SirSundays/capactive-soil-moisture-sensor-lora/Media/PCB.jpg

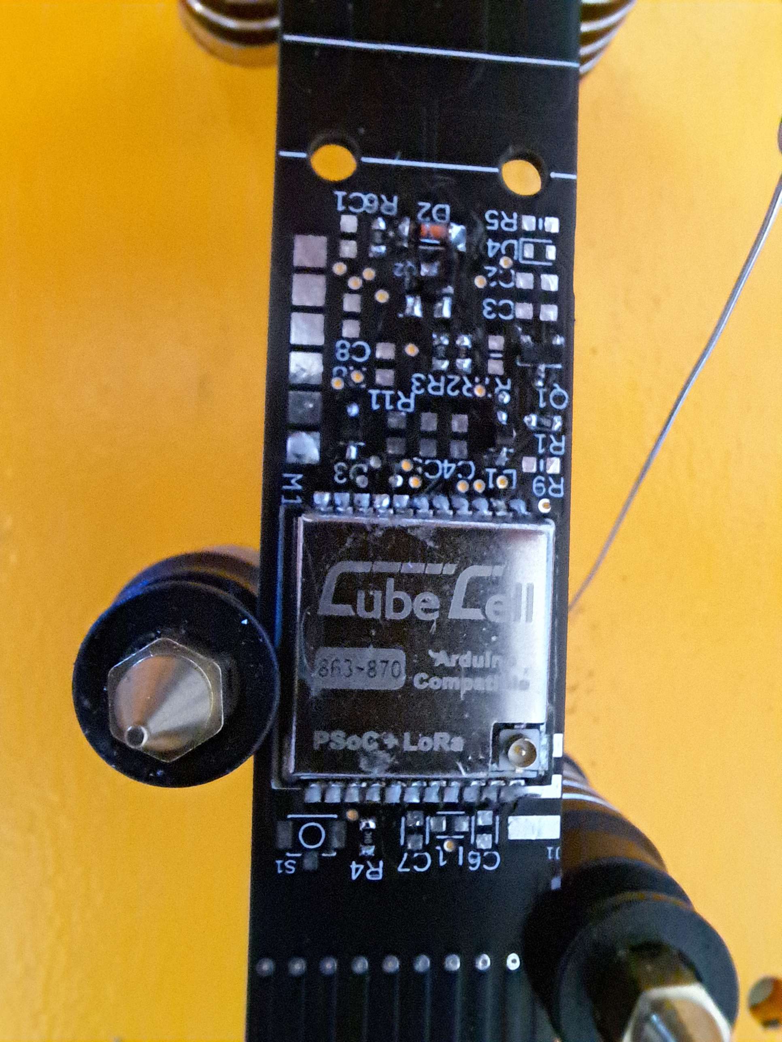
Media/PCB.jpg
