SirSundays/capactive-soil-moisture-sensor-lora/Media/Potting/20230603_204240.jpg

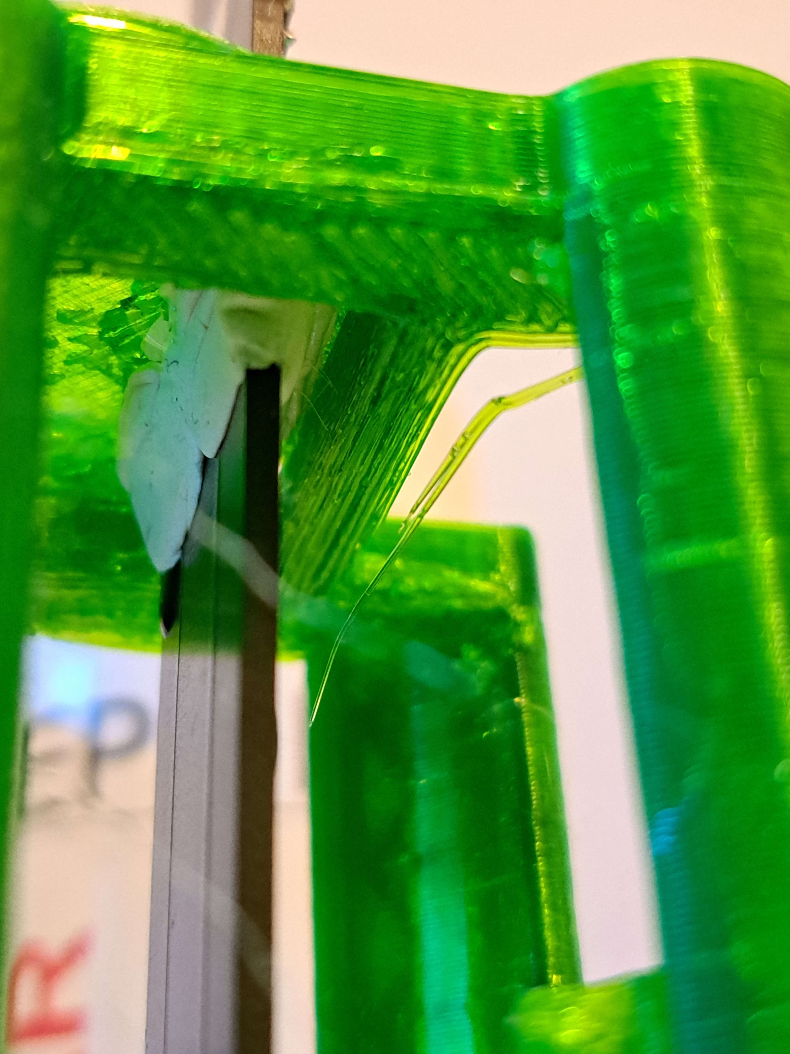
Media/Potting/20230603_204240.jpg
