SirSundays/capactive-soil-moisture-sensor-lora/Media/Potting/20230606_083855.jpg

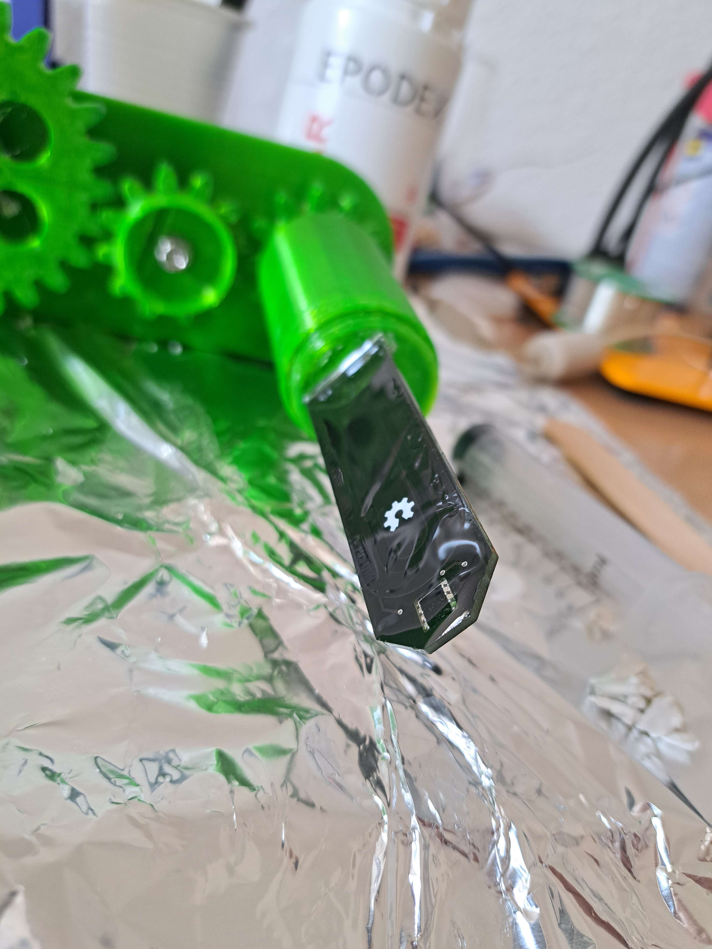
Media/Potting/20230606_083855.jpg
