SirSundays/capactive-soil-moisture-sensor-lora/Media/Potting/20230606_083947.jpg

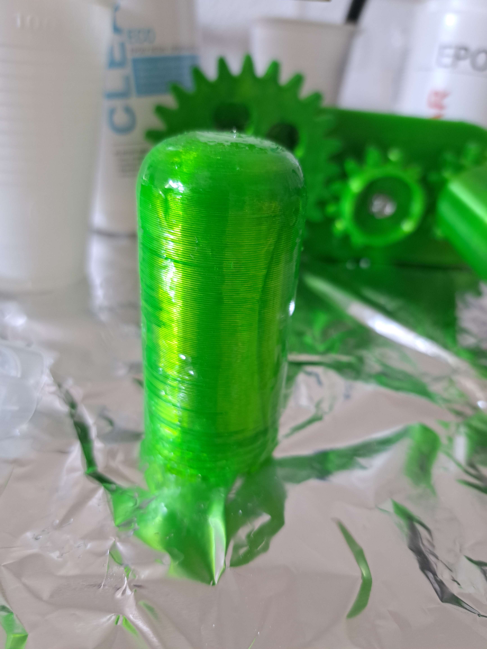
Media/Potting/20230606_083947.jpg
