SirSundays/capactive-soil-moisture-sensor-lora/Media/Potting/20240121_231839.jpg

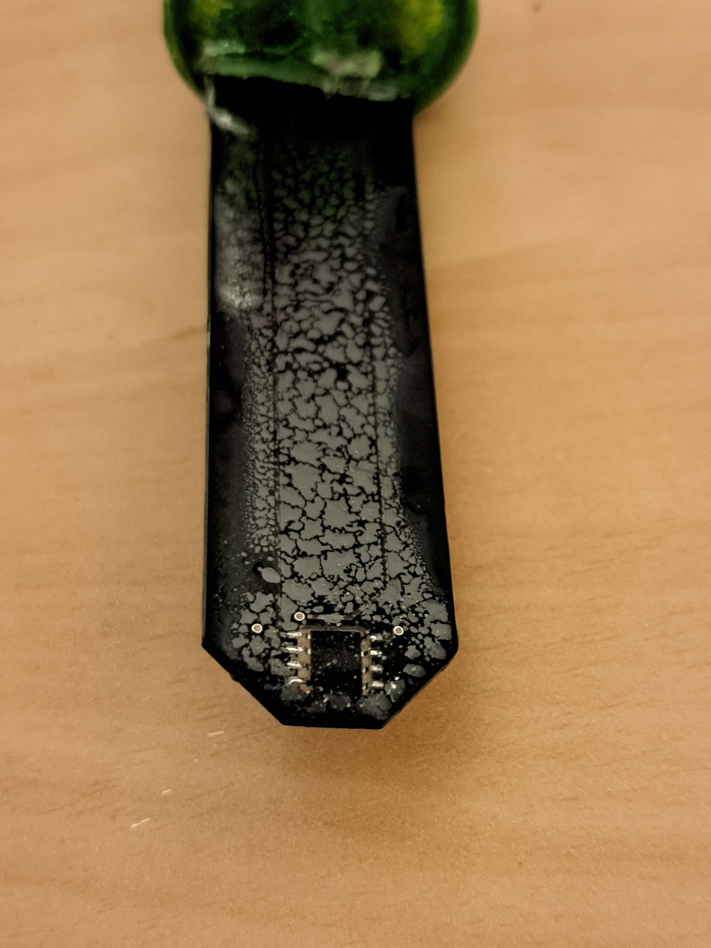
Media/Potting/20240121_231839.jpg
