SirSundays/capactive-soil-moisture-sensor-lora/Media/Potting/20240121_233238.jpg

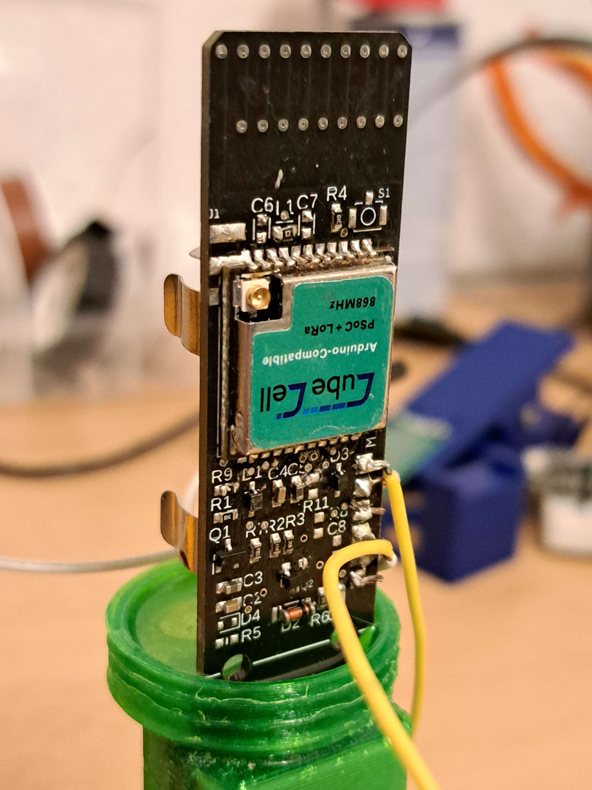
Media/Potting/20240121_233238.jpg
