SirSundays/capactive-soil-moisture-sensor-lora/Media/Potting/PCB.jpg

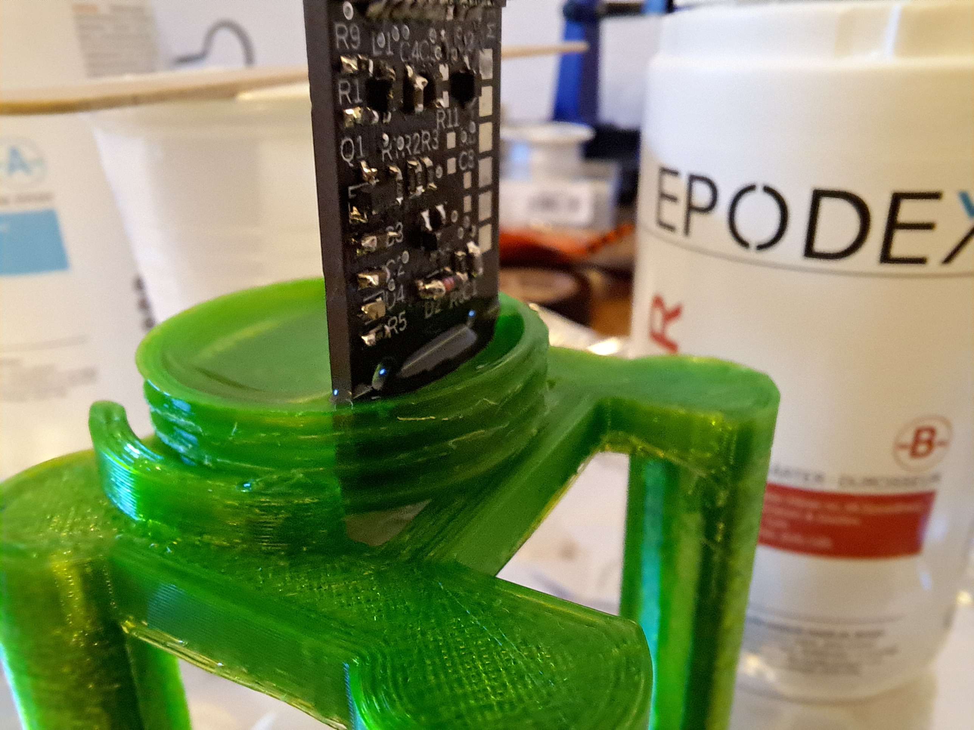
Media/Potting/PCB.jpg
