SirSundays/capactive-soil-moisture-sensor-lora/Media/Programming_Jig.jpg

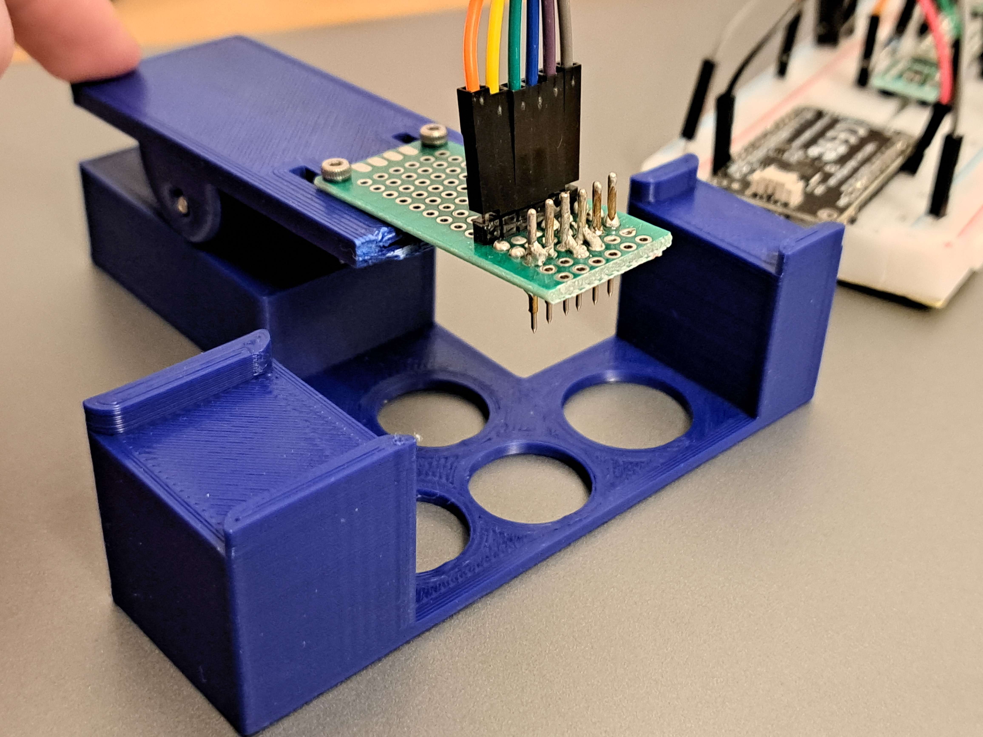
Media/Programming_Jig.jpg
