SirSundays/capactive-soil-moisture-sensor-lora/Media/Antenna Test/20230517_183743.jpg

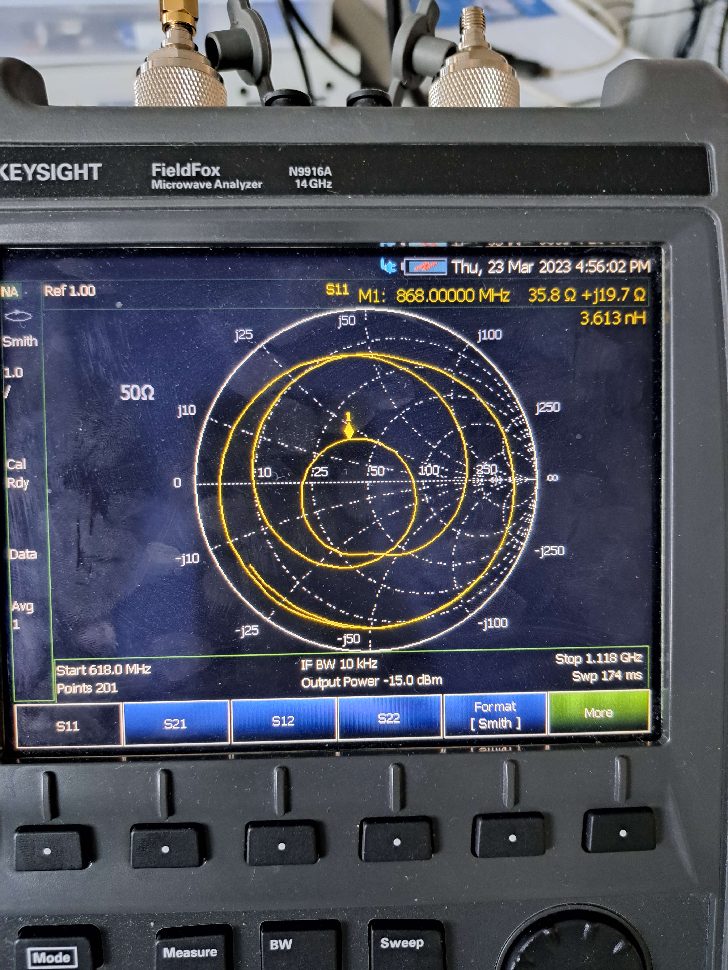
Media/Antenna Test/20230517_183743.jpg
