SirSundays/capactive-soil-moisture-sensor-lora/Media/Antenna Test/20230517_183756.jpg

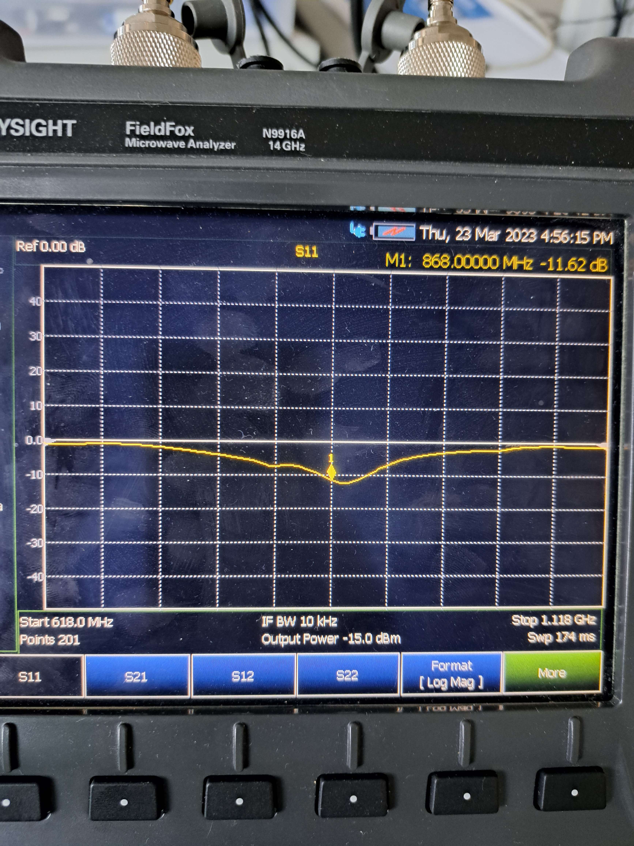
Media/Antenna Test/20230517_183756.jpg
