SirSundays/capactive-soil-moisture-sensor-lora/Media/Antenna Test/20230517_184227.jpg

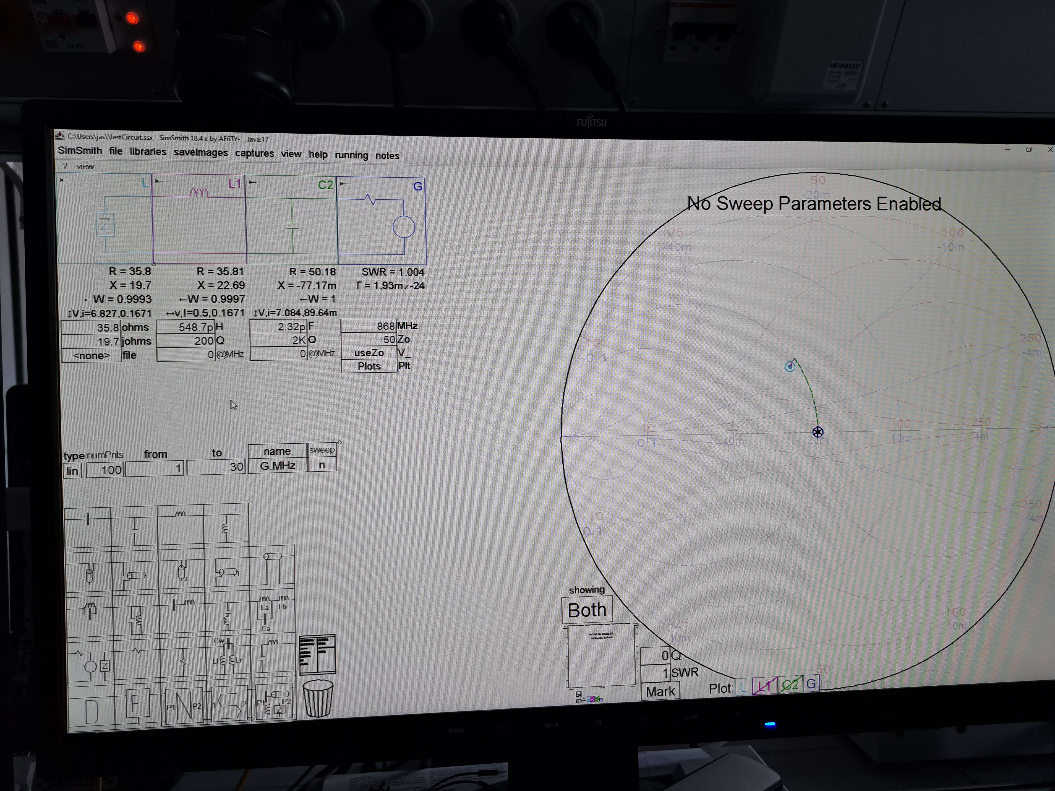
Media/Antenna Test/20230517_184227.jpg
