SirSundays/capactive-soil-moisture-sensor-lora/Media/Antenna Test/20230517_184956.jpg

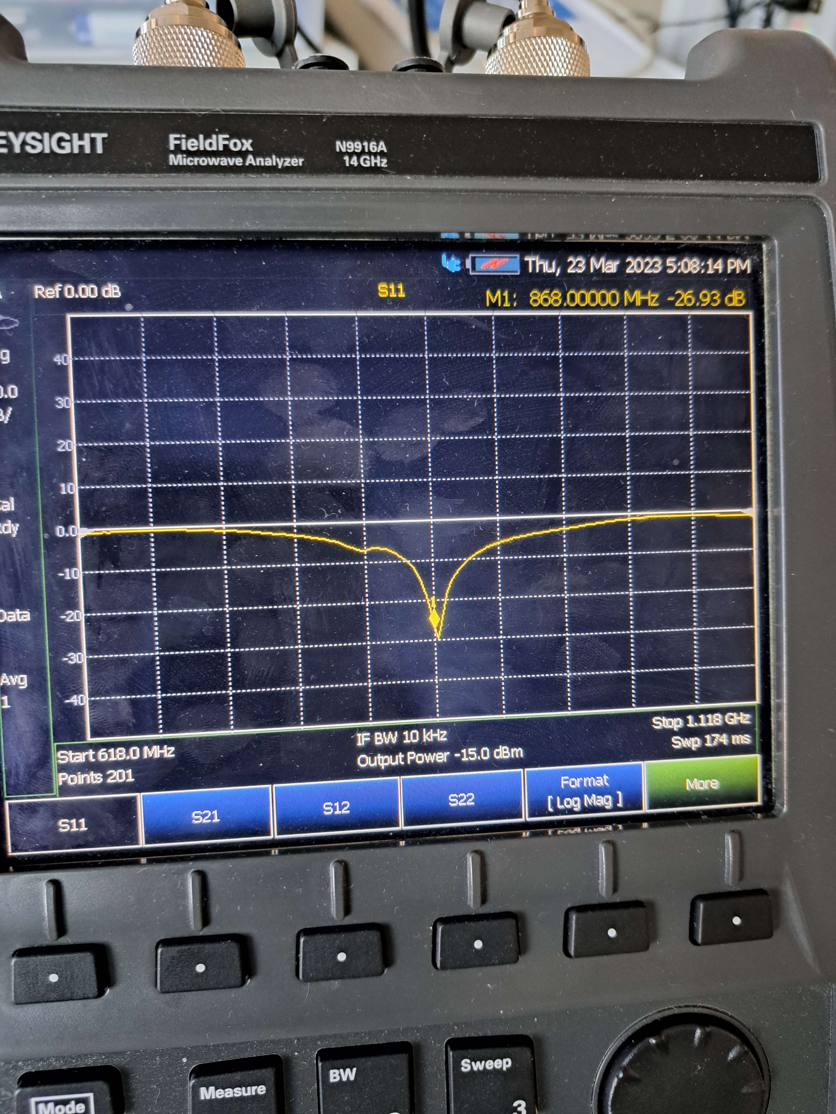
Media/Antenna Test/20230517_184956.jpg
