SirSundays/capactive-soil-moisture-sensor-lora/Media/Antenna Test/20230517_185003.jpg

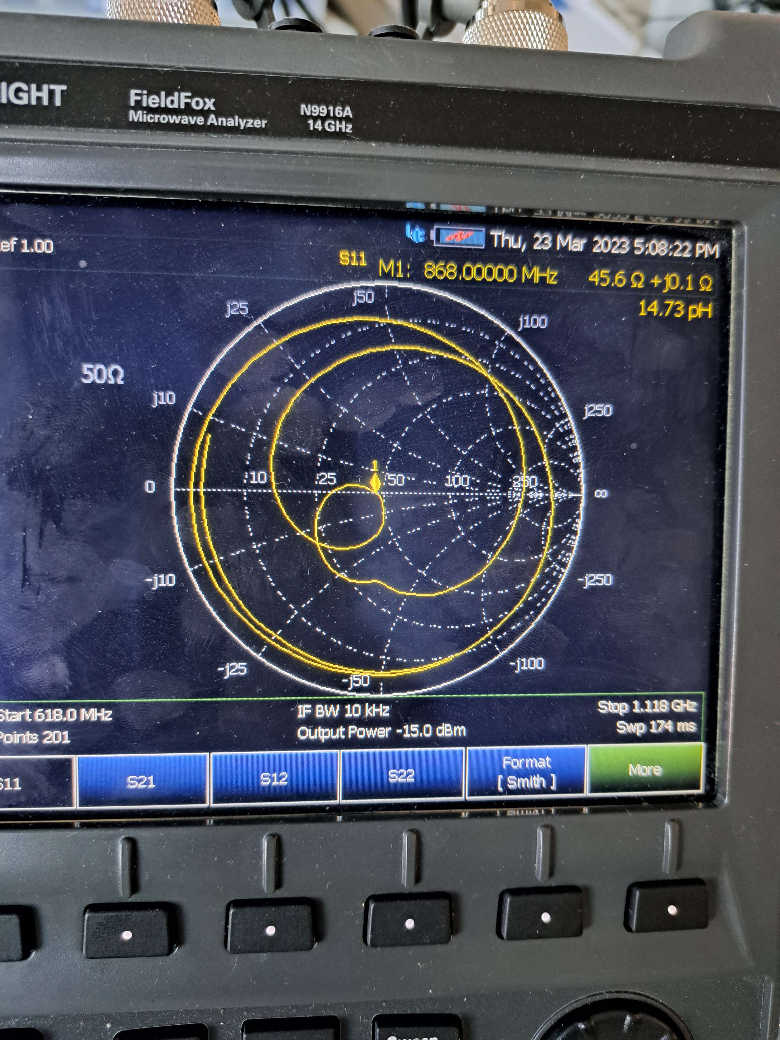
Media/Antenna Test/20230517_185003.jpg
