SirSundays/capactive-soil-moisture-sensor-lora/Media/Antenna Test/20240121_233658.jpg

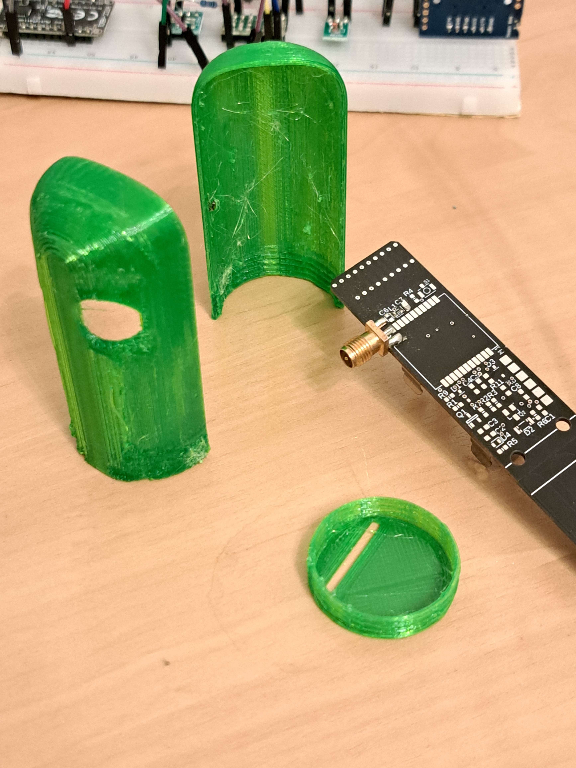
Media/Antenna Test/20240121_233658.jpg
