SirSundays/capactive-soil-moisture-sensor-lora/Media/Battery Test/20240121_231822.jpg

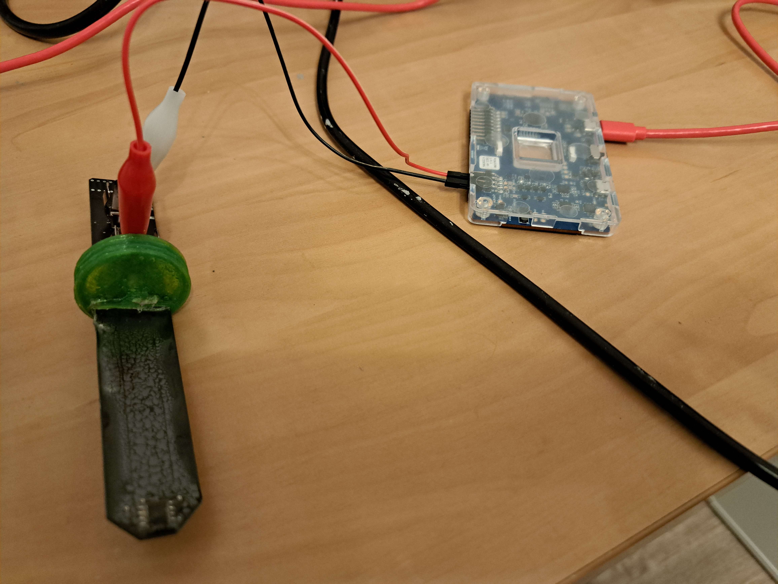
Media/Battery Test/20240121_231822.jpg
