SirSundays/capactive-soil-moisture-sensor-lora/Media/Battery Test/20240121_233023.jpg

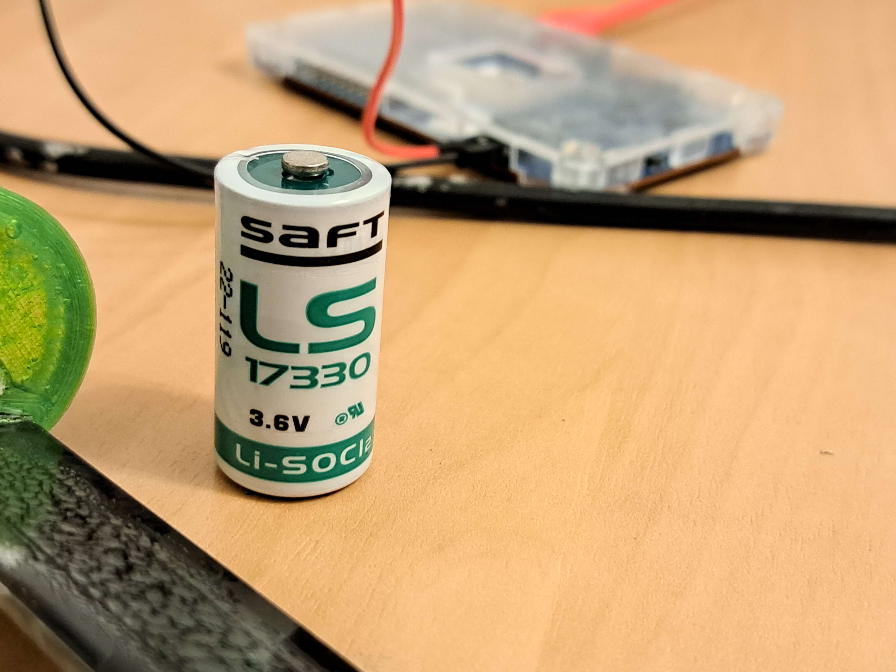
Media/Battery Test/20240121_233023.jpg
