SirSundays/capactive-soil-moisture-sensor-lora/Media/Circuit Evaluation/20230502_162933.jpg

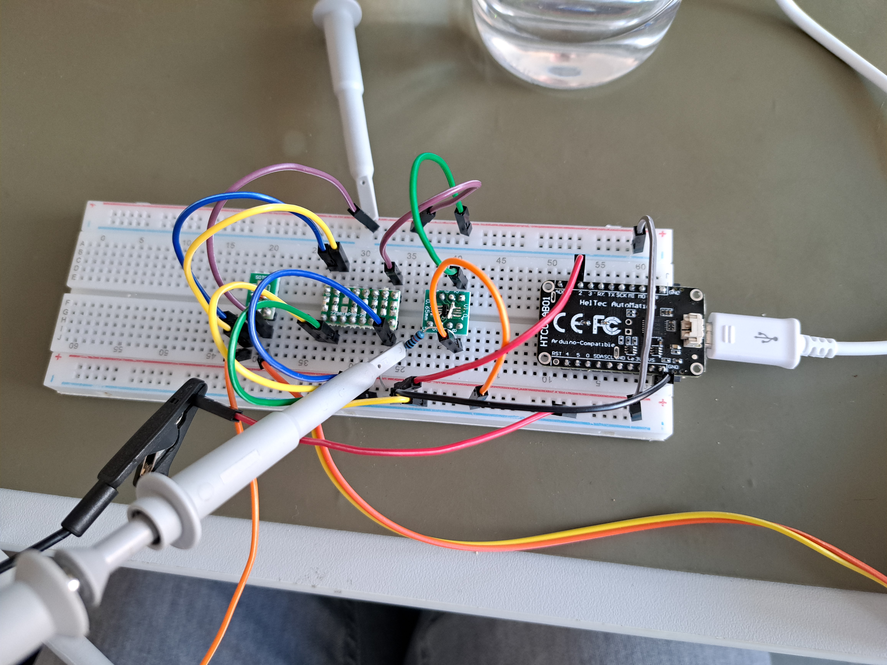
Media/Circuit Evaluation/20230502_162933.jpg
