SirSundays/capactive-soil-moisture-sensor-lora/Media/Circuit Evaluation/20230502_163412.jpg

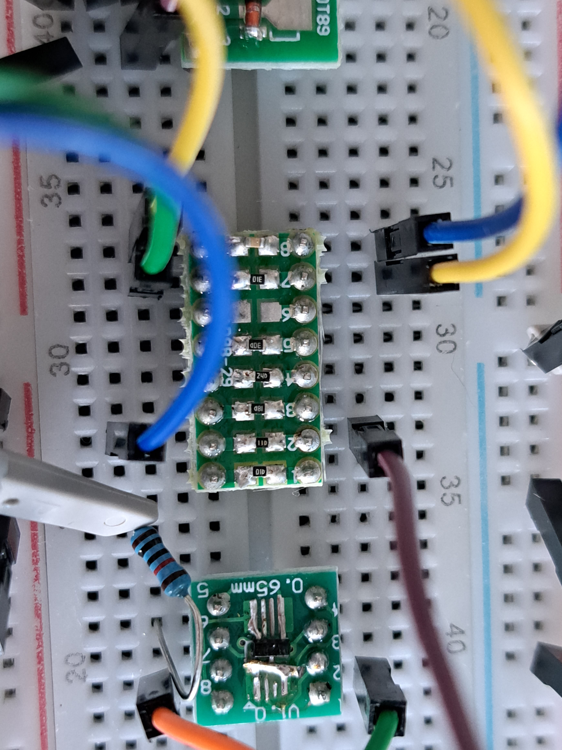
Media/Circuit Evaluation/20230502_163412.jpg
