SirSundays/capactive-soil-moisture-sensor-lora/Media/First PCB Tests/20230424_172208.jpg

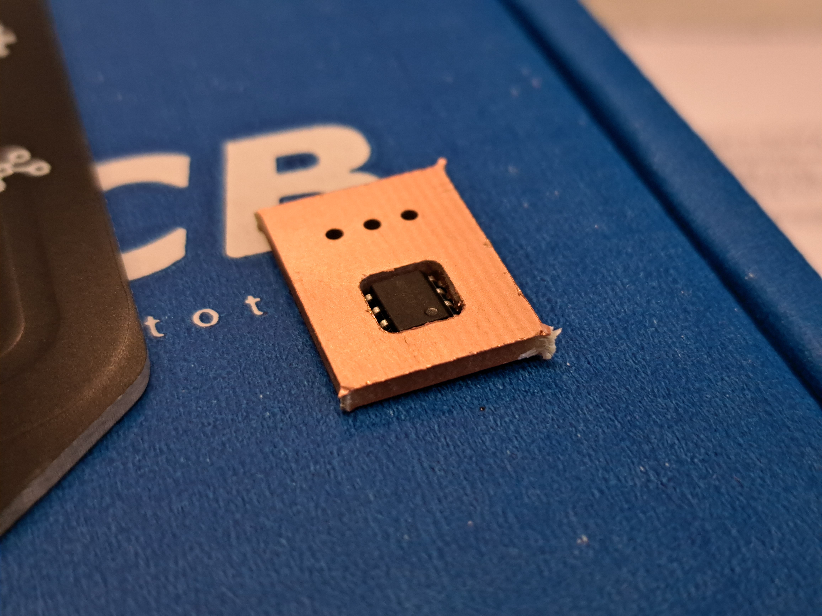
Media/First PCB Tests/20230424_172208.jpg
