SirSundays/capactive-soil-moisture-sensor-lora/Media/First PCB Tests/20230424_172226.jpg

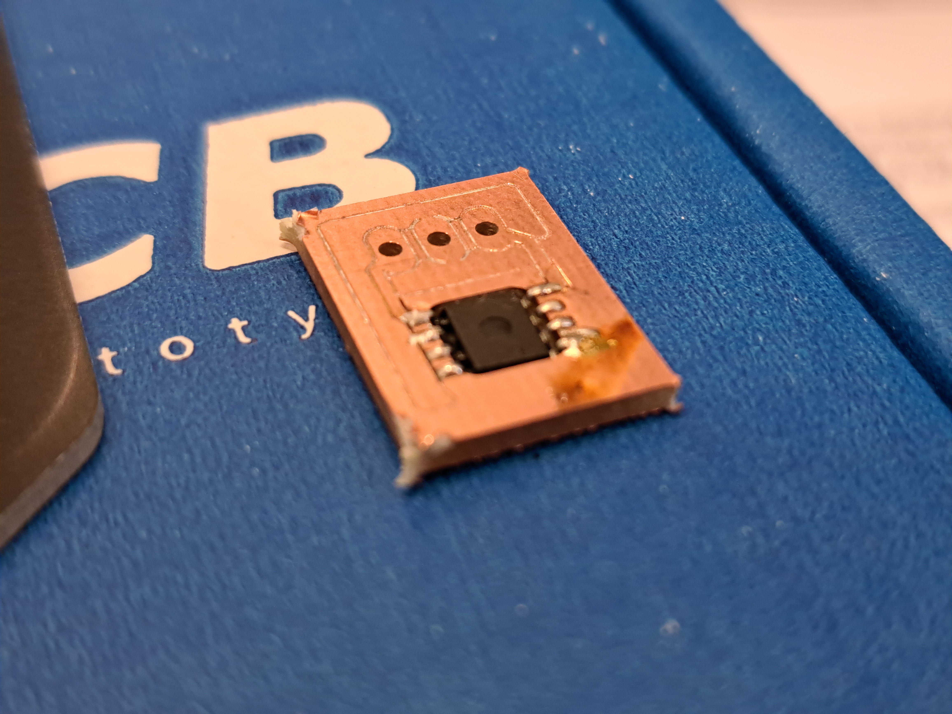
Media/First PCB Tests/20230424_172226.jpg
