SirSundays/capactive-soil-moisture-sensor-lora/Media/First PCB Tests/IoT-Battery Calculator Prototype.png

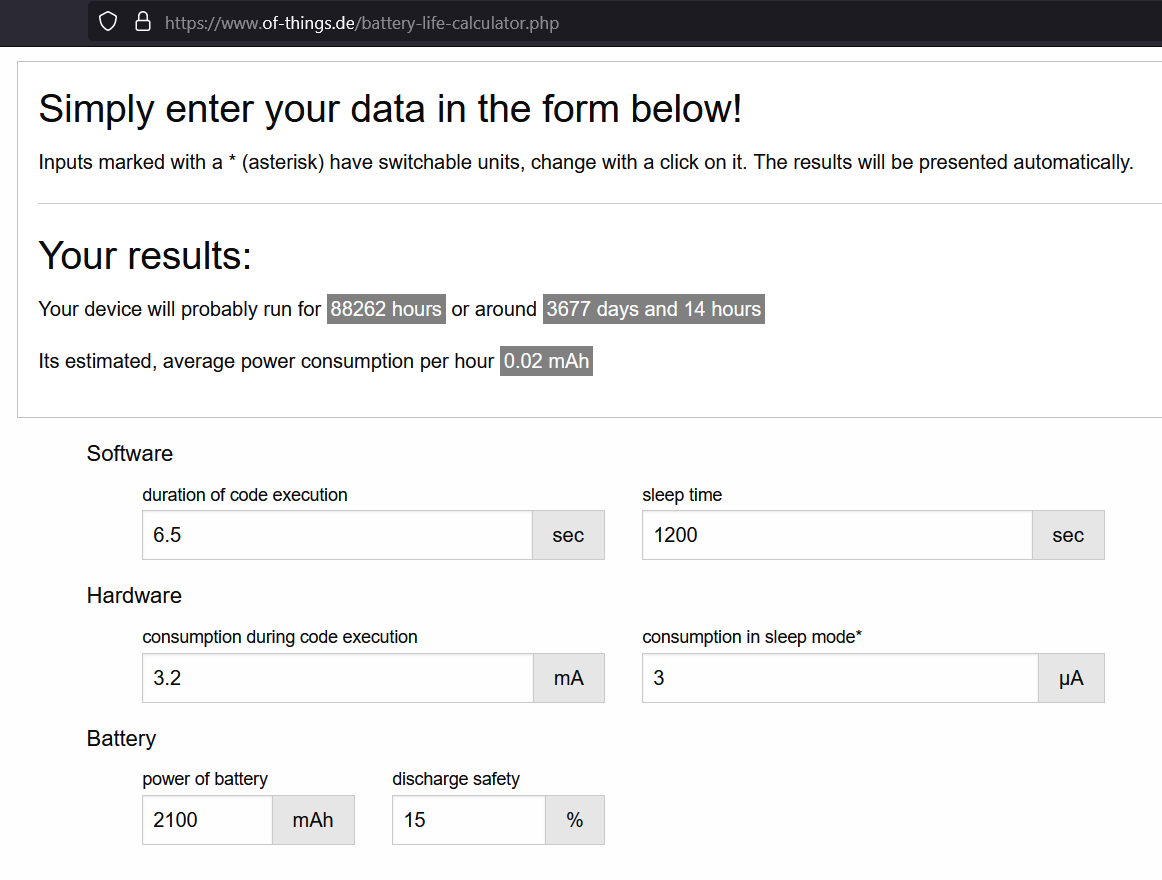
Media/First PCB Tests/IoT-Battery Calculator Prototype.png
