SirSundays/capactive-soil-moisture-sensor-lora/Media/First PCB Tests/SF8BW125 Prototype.png

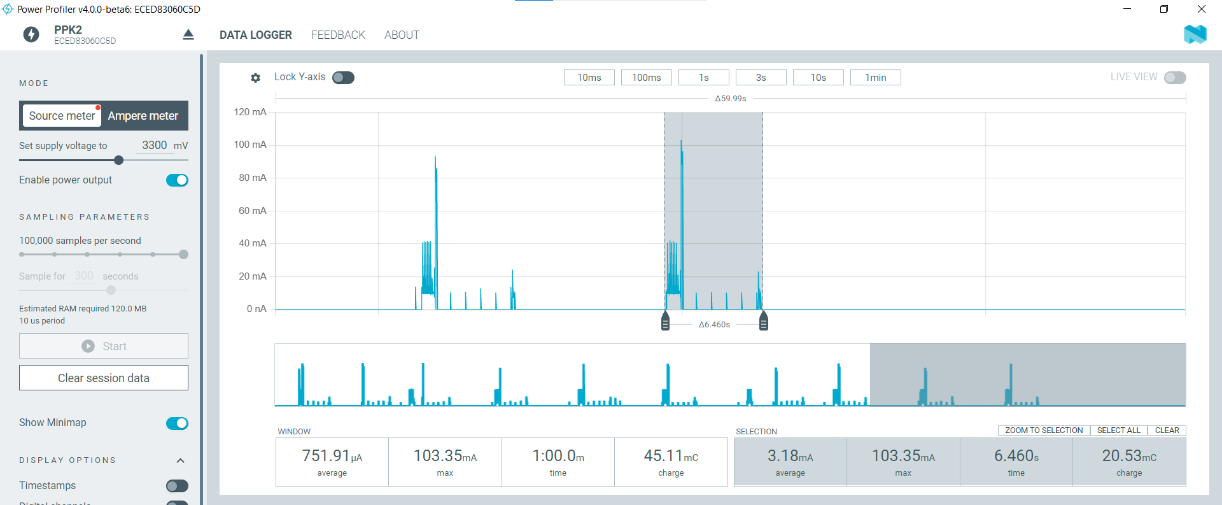
Media/First PCB Tests/SF8BW125 Prototype.png
